terrabite3/68k-nano/src/cf.h

#pragma once

#include "type.h"

// Buffers for CompactFlash should usually be the size of one sector, 512 bytes.
// The buffer_len argument is the number of WORDS, not the number of BYTES!

static const uint16_t SECTOR_BUFFER_LEN = 256;


uint16_t cf_identify(uint16_t* buffer, uint16_t buffer_len);

// Sector 1 is the first sector -- don't try to read sector 0
uint16_t cf_read_sector(uint32_t sector, uint16_t* buffer, uint16_t buffer_len);
